svenpetersen1965/PET-IEEE-488-Extension/Base/Rev. 0/pictures/7518_-_IEEE_ribbon_cable_connectors.JPG

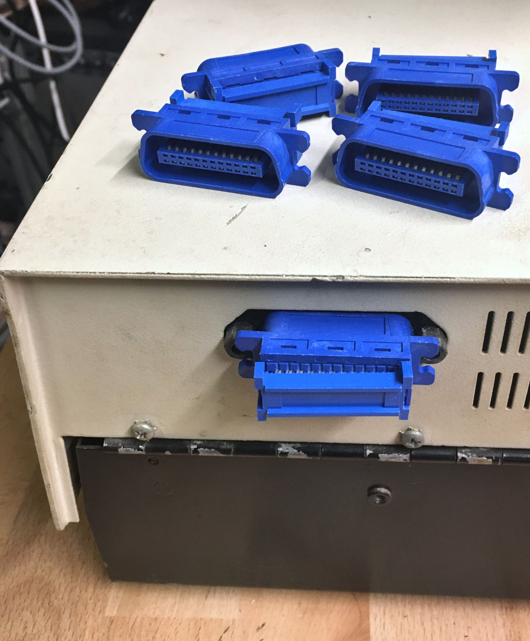
Base/Rev. 0/pictures/7518_-_IEEE_ribbon_cable_connectors.JPG
