svenpetersen1965/PET-IEEE-488-Extension/Base_Centronics/case/Rev.0/label/label.png

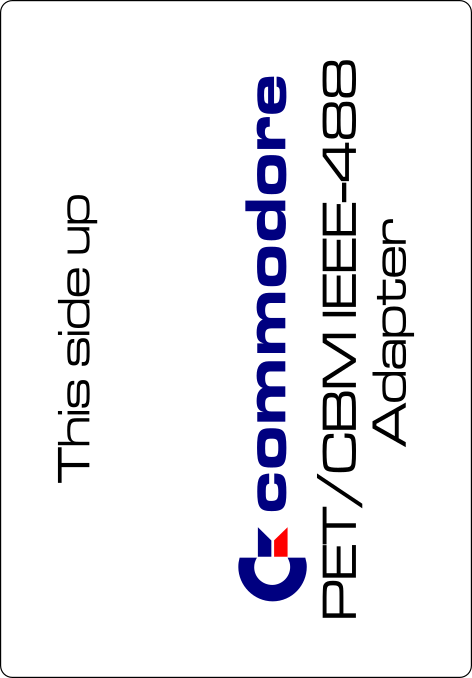
Base_Centronics/case/Rev.0/label/label.png
