svenpetersen1965/PET-IEEE-488-Extension/Base_Centronics/Rev. 0/pictures/2979_-_IEEE488_Riser_cable_fit.JPG

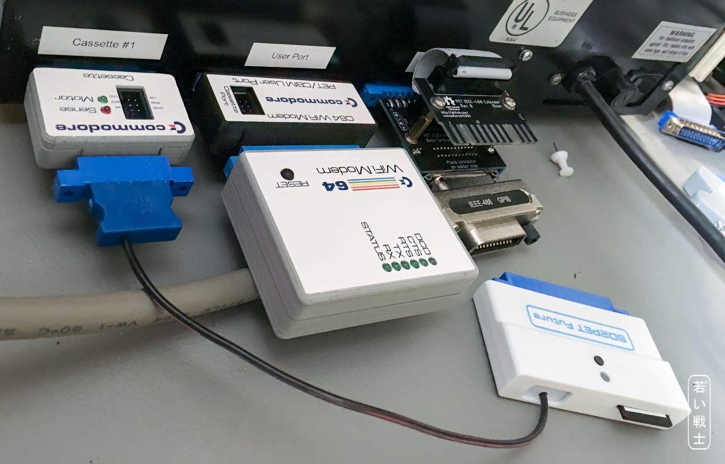
Base_Centronics/Rev. 0/pictures/2979_-_IEEE488_Riser_cable_fit.JPG
