svenpetersen1965/PET-IEEE-488-Extension/Base_Centronics/Rev. 0/pictures/3082_-_Base_Centr_in_Case.JPG

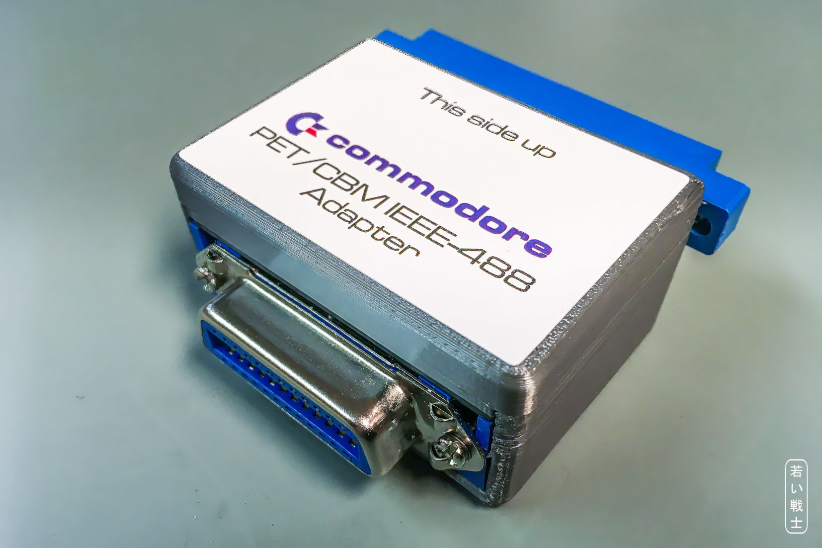
Base_Centronics/Rev. 0/pictures/3082_-_Base_Centr_in_Case.JPG
