svenpetersen1965/PET-IEEE-488-Extension/Riser/Rev. 0/pictures/dimensions.png

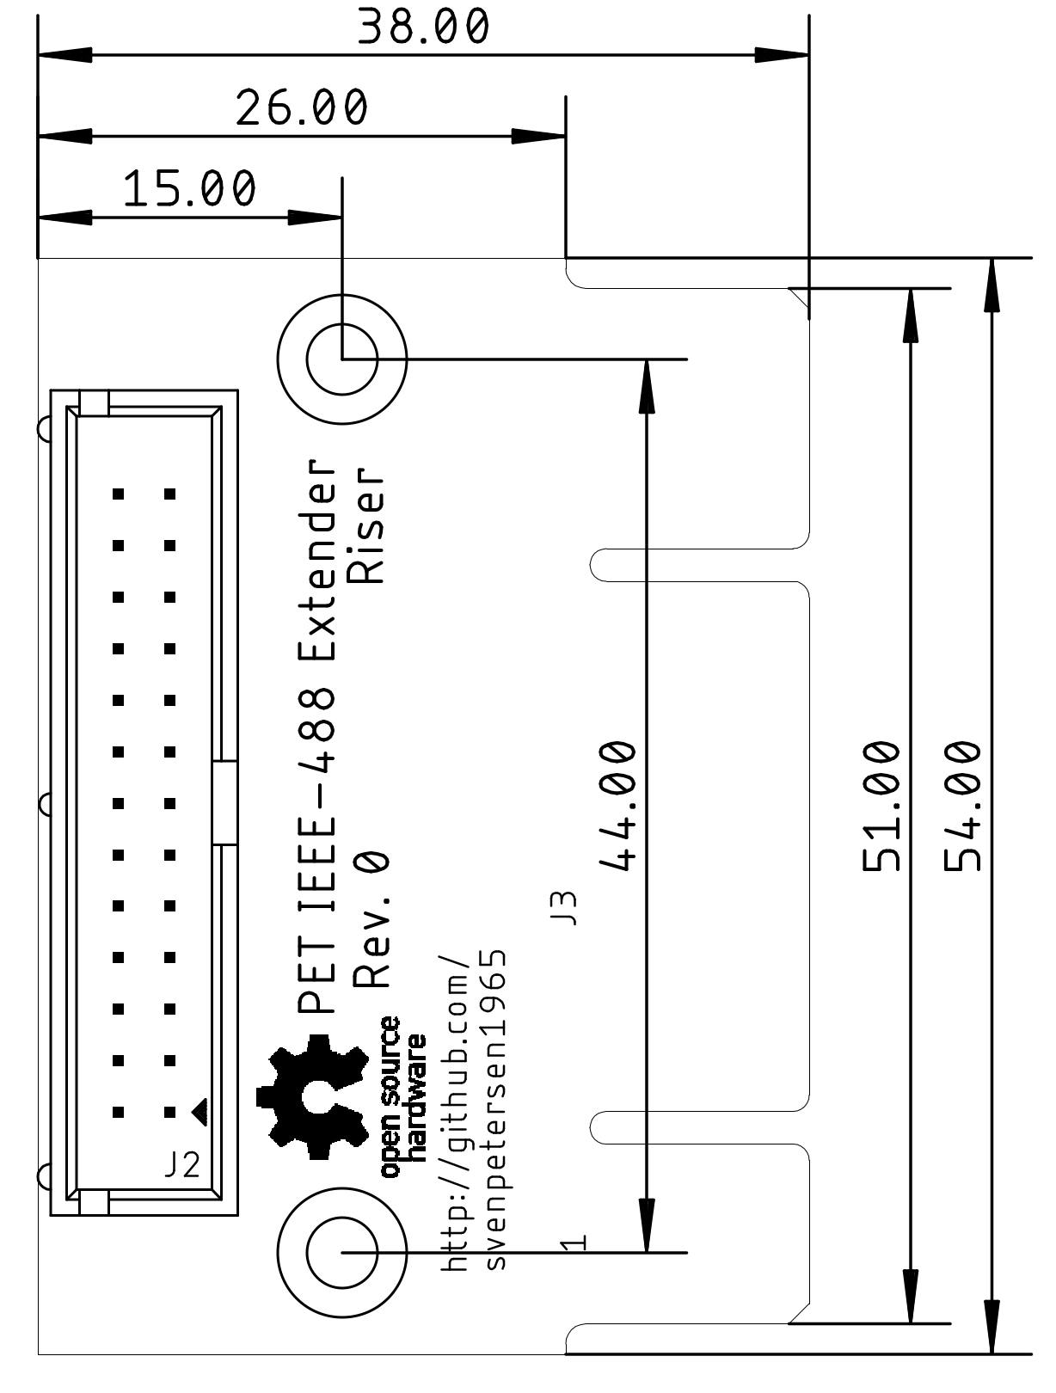
Riser/Rev. 0/pictures/dimensions.png
